Owen-Ball/Electronic-Load/CAD/prints/front_panel.3MF

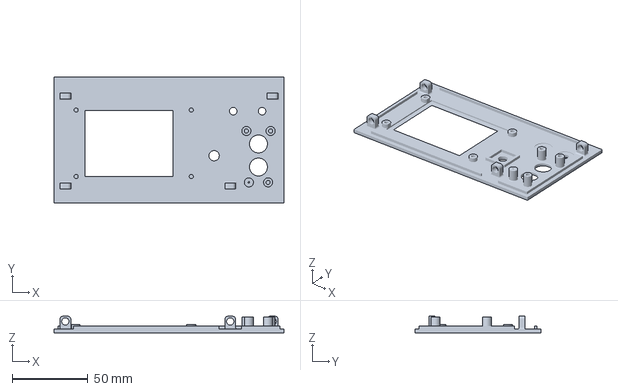
[picture p5: CAD file, 2024-12-24]
CAD/prints/front_panel.3MF
152.0 x 83.6 x 11.0 mm
