Owen-Ball/Electronic-Load/FilterBoard/PCB/Gerbers/filter_board-F_Cu.dxf

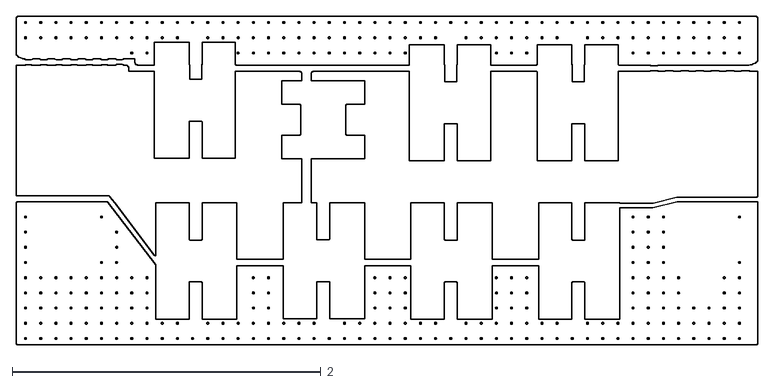
[picture p6: CAD file, 2025-03-30]
FilterBoard/PCB/Gerbers/filter_board-F_Cu.dxf
4.80 x 2.13
