Owen-Ball/Electronic-Load/CAD/prints/switch.SLDPRT

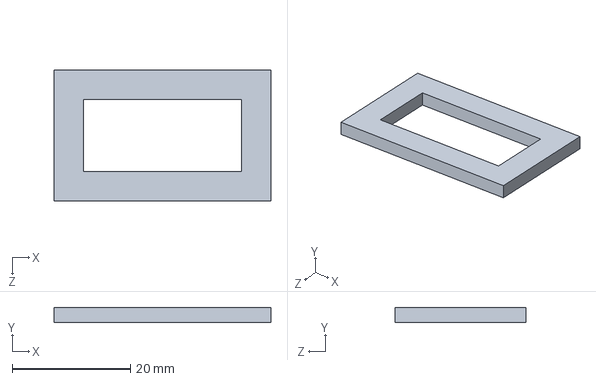
[picture p7: CAD file, 2024-12-24]
CAD/prints/switch.SLDPRT
36.8 x 2.50 x 22.2 mm
