Owen-Ball/Electronic-Load/CAD/Screen/front_glass.SLDPRT

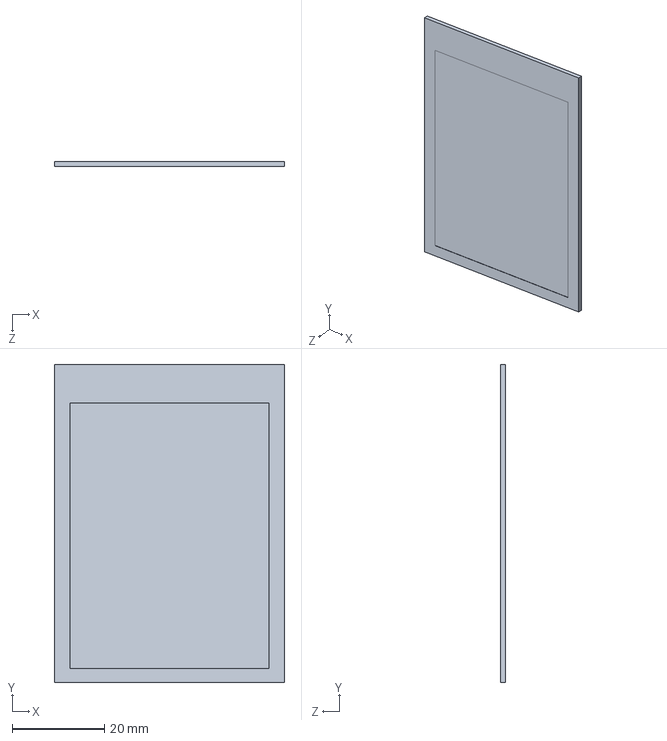
[picture p8: CAD file, 2024-12-24]
CAD/Screen/front_glass.SLDPRT
50.0 x 69.0 x 1.16 mm
