Owen-Ball/Electronic-Load/CAD/outer_shell.SLDPRT

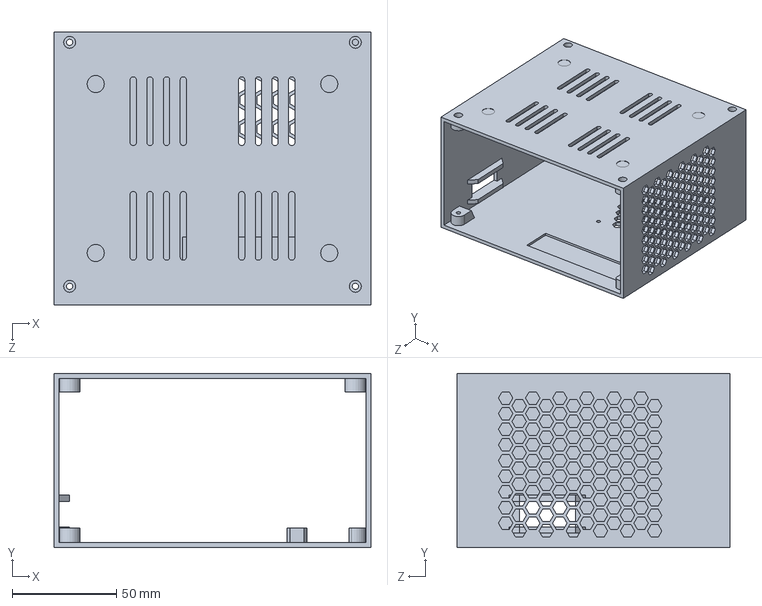
[picture p9: CAD file, 2024-12-24]
CAD/outer_shell.SLDPRT
152.0 x 83.6 x 131.0 mm
