Owen-Ball/Electronic-Load/CAD/Heatsink.SLDPRT

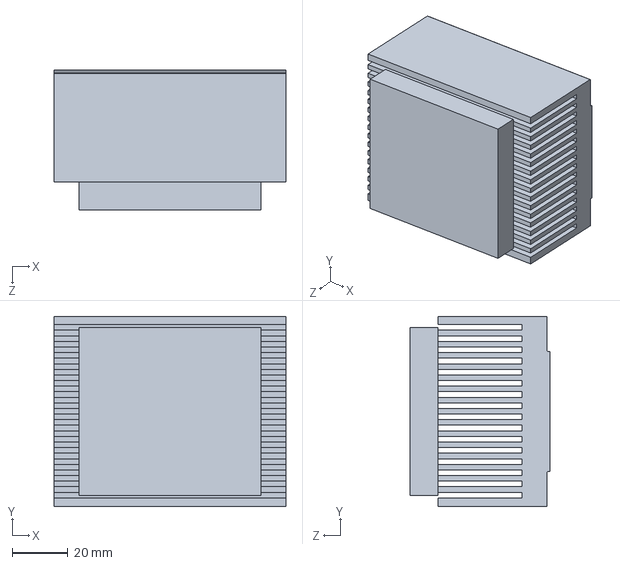
[picture p10: CAD file, 2024-12-24]
CAD/Heatsink.SLDPRT
83.0 x 68.0 x 50.0 mm
