Owen-Ball/Electronic-Load/CAD/front_trim.SLDPRT

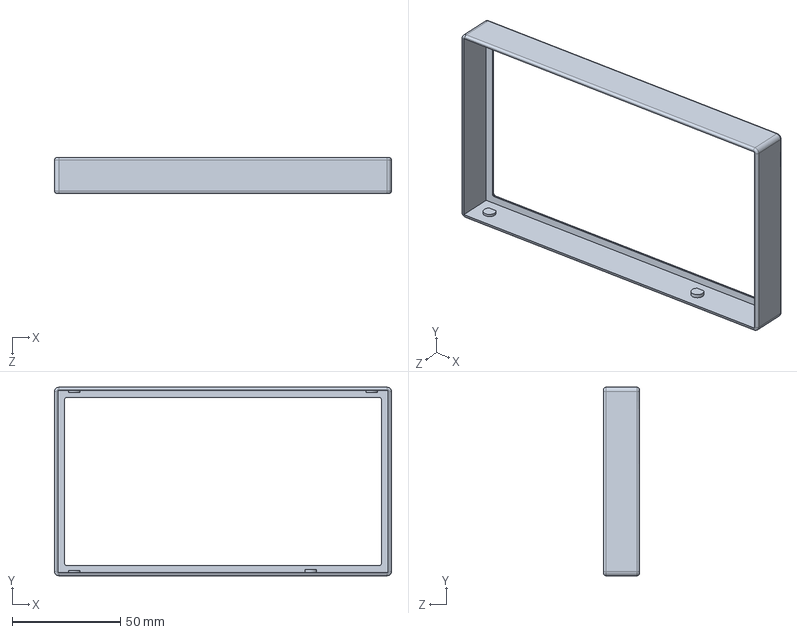
[picture p11: CAD file, 2024-12-24]
CAD/front_trim.SLDPRT
155.4 x 87.0 x 16.5 mm
