Owen-Ball/Electronic-Load/CAD/Knob.SLDPRT

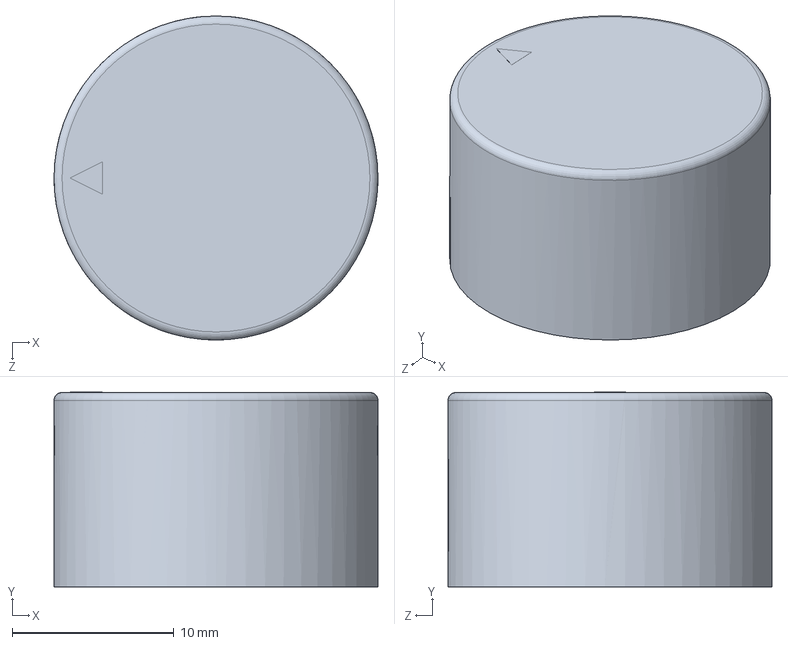
[picture p12: CAD file, 2024-12-24]
CAD/Knob.SLDPRT
20.0 x 12.0 x 20.0 mm
