Owen-Ball/Electronic-Load/CAD/RS-25-12.SLDPRT

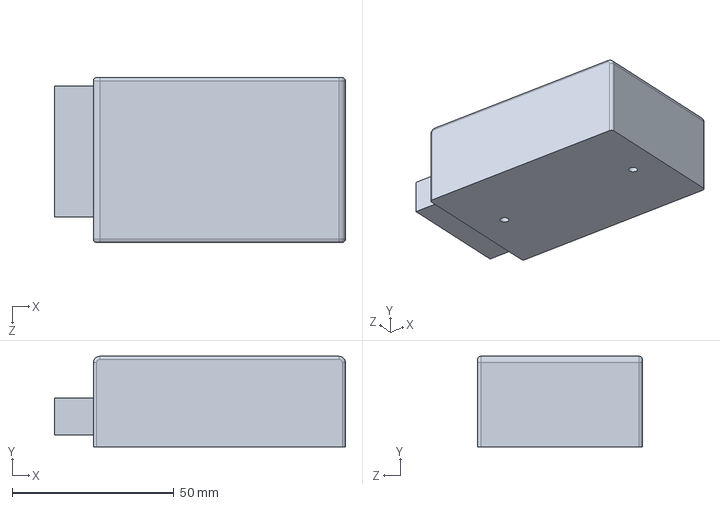
[picture p13: CAD file, 2024-12-24]
CAD/RS-25-12.SLDPRT
90.0 x 28.0 x 51.0 mm
