Owen-Ball/Electronic-Load/CAD/Fan.SLDPRT

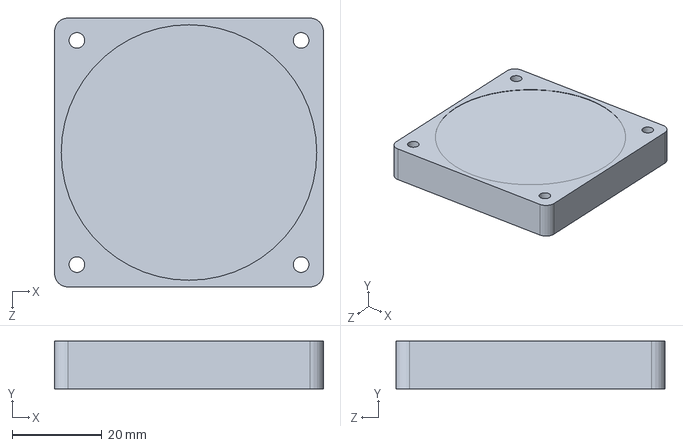
[picture p14: CAD file, 2024-12-24]
CAD/Fan.SLDPRT
60.0 x 10.6 x 60.0 mm
