Owen-Ball/Electronic-Load/CAD/BindingPost.SLDPRT

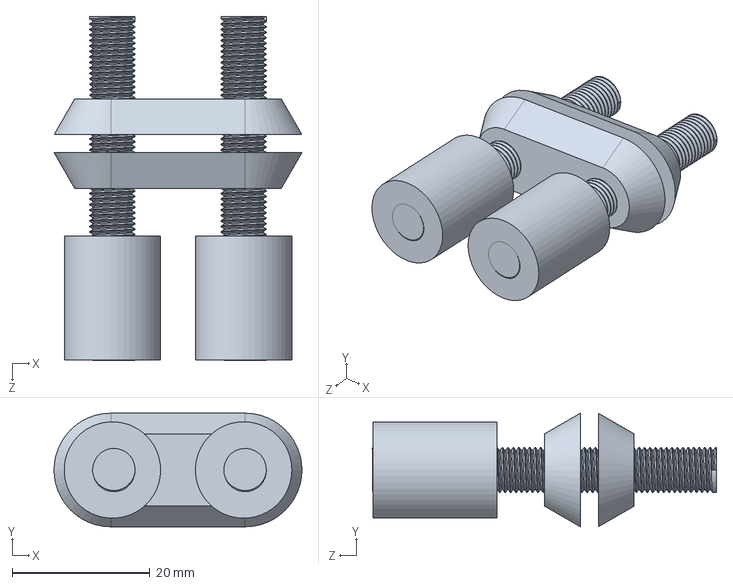
[picture p15: CAD file, 2024-12-24]
CAD/BindingPost.SLDPRT
36.0 x 16.5 x 50.0 mm
