Owen-Ball/Electronic-Load/CAD/button.SLDPRT

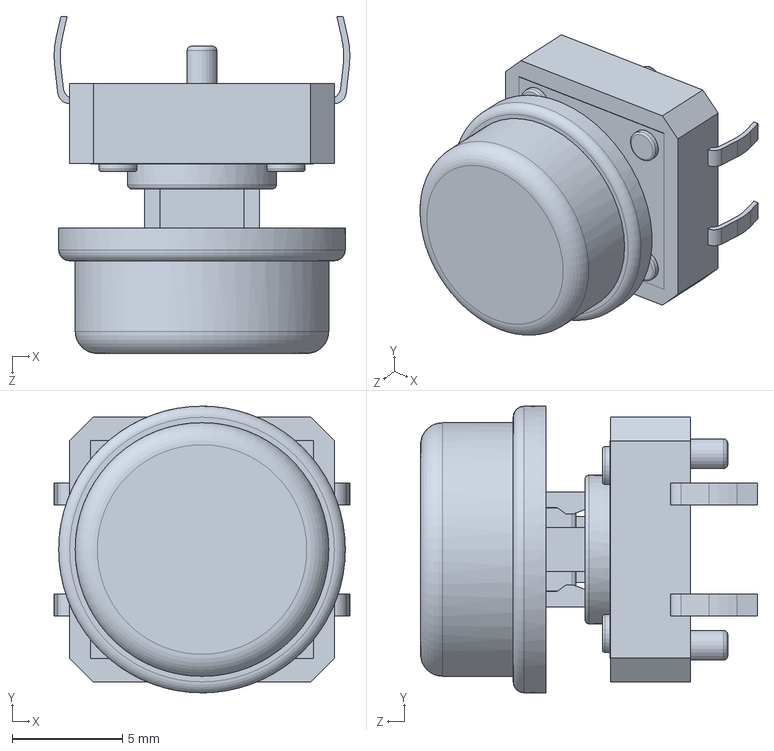
[picture p16: CAD file, 2024-12-24]
CAD/button.SLDPRT
13.4 x 13.0 x 15.3 mm
