Owen-Ball/Electronic-Load/CAD/perfboard.SLDPRT

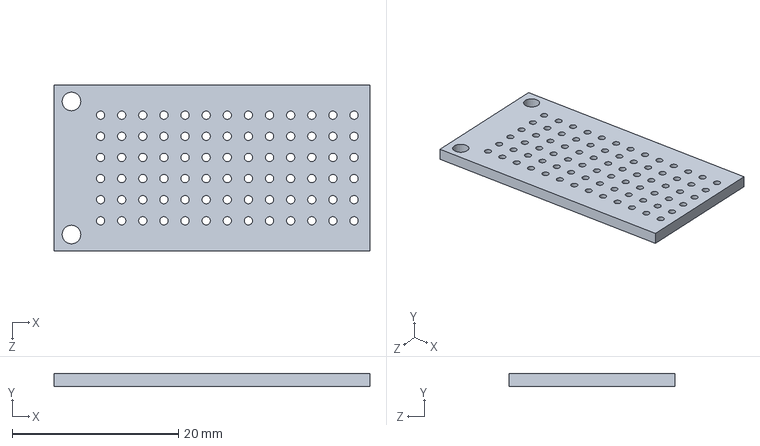
[picture p17: CAD file, 2024-12-24]
CAD/perfboard.SLDPRT
38.0 x 1.60 x 20.0 mm
