Owen-Ball/Electronic-Load/CAD/top.SLDPRT

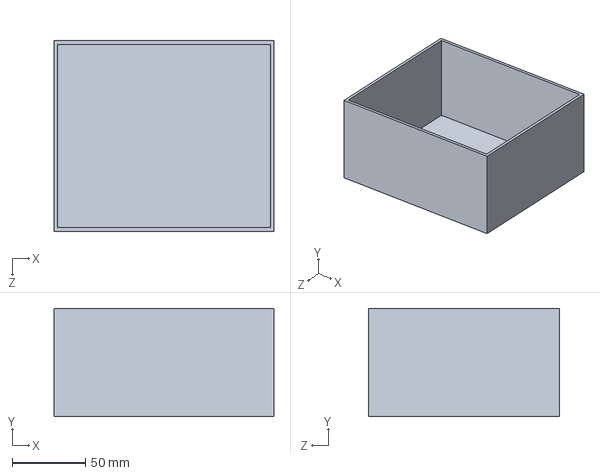
[picture p18: CAD file, 2024-12-24]
CAD/top.SLDPRT
150.5 x 74.1 x 130.5 mm
