Owen-Ball/Electronic-Load/CAD/back_panel.SLDPRT

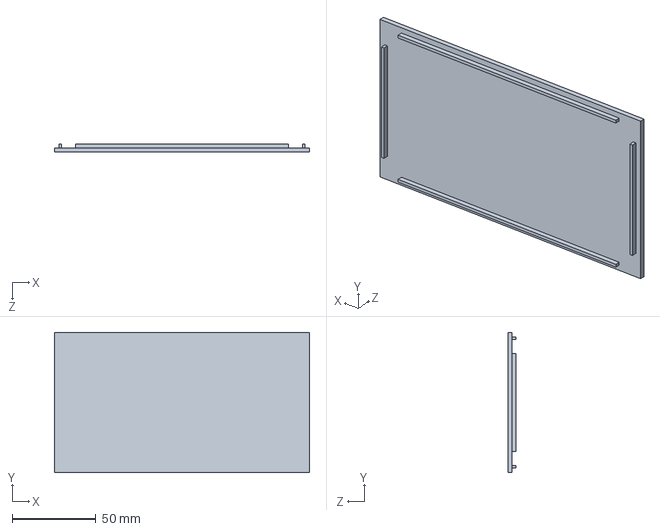
[picture p19: CAD file, 2024-12-24]
CAD/back_panel.SLDPRT
152.0 x 83.6 x 5.00 mm
