Owen-Ball/Electronic-Load/CAD/IEC320-C14RCPT.SLDPRT

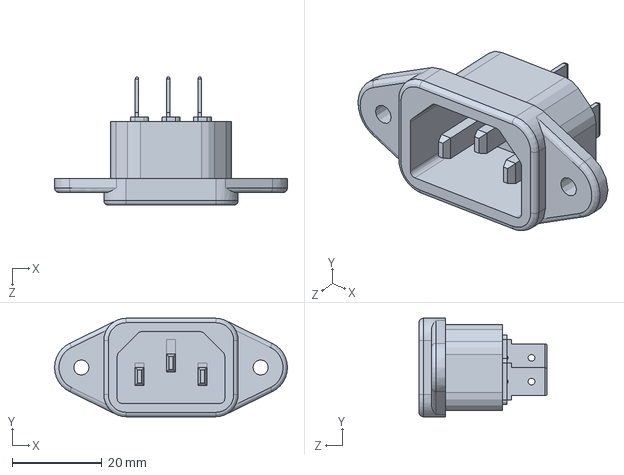
[picture p20: CAD file, 2024-12-24]
CAD/IEC320-C14RCPT.SLDPRT
52.0 x 22.0 x 28.6 mm
