Owen-Ball/Electronic-Load/CAD/encoder.SLDPRT

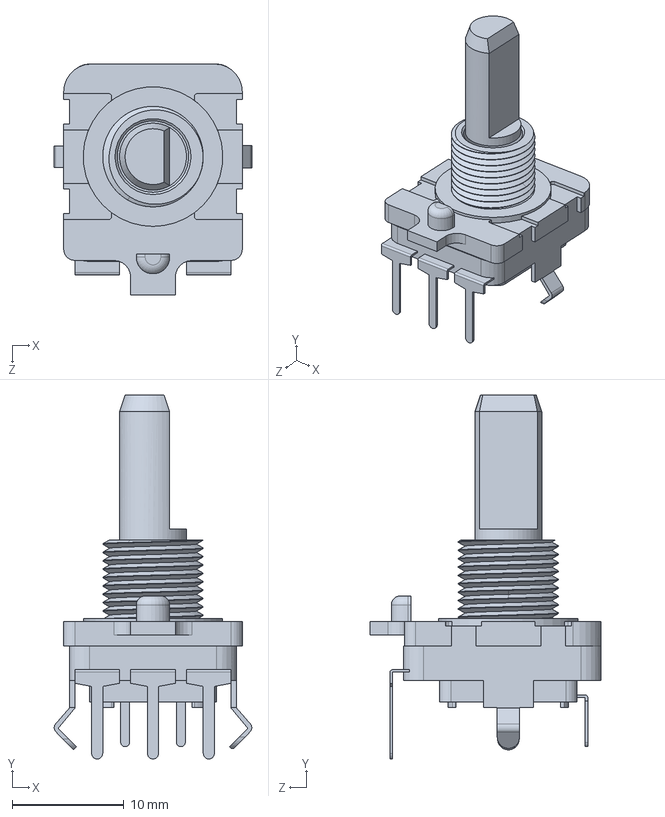
[picture p21: CAD file, 2024-12-24]
CAD/encoder.SLDPRT
17.7 x 32.6 x 20.7 mm
