Owen-Ball/Electronic-Load/Firmware/eload/debug_utils.h

/*
https://forum.arduino.cc/t/serial-debug-macro/64259/3
*/

//#define DEBUG

#ifndef DEBUGUTILS_H
#define DEBUGUTILS_H

#ifdef DEBUG
  #define DEBUG_PRINT(...) Serial.print(__VA_ARGS__)
  #define DEBUG_PRINTLN(...) Serial.println(__VA_ARGS__)
#else
  #define DEBUG_PRINT(...)
  #define DEBUG_PRINTLN(...)
#endif

#endif
